tepasha/alertinua/alertinua-c/components/map/ukraine_map_data.h

#pragma once
#include <stdint.h>

typedef struct { uint8_t x, y; } map_point_t;

typedef struct {
    const char *name;   // Ukrainian name (UTF-8), for logging only (no Cyrillic glyphs on screen)
    uint16_t point_offset;
    uint8_t  point_count;
    uint16_t color;     // RGB565, NOT byte-swapped yet
} map_region_t;

#define MAP_NUM_POINTS 921
static const map_point_t map_points[MAP_NUM_POINTS] = {
    {100,56}, {104,56}, {104,60}, {106,62}, {105,65}, {109,70}, {109,73}, {110,73}, {107,74}, {106,78},
    {100,77}, {98,79}, {97,78}, {95,77}, {94,79}, {94,77}, {93,77}, {93,76}, {91,76}, {88,73},
    {85,73}, {84,70}, {84,66}, {85,63}, {89,63}, {87,58}, {88,54}, {97,53}, {98,52}, {100,56},
    {66,23}, {67,23}, {66,26}, {67,27}, {66,31}, {69,30}, {71,33}, {70,35}, {71,36}, {70,37},
    {70,38}, {69,39}, {69,41}, {67,40}, {64,41}, {64,42}, {62,43}, {63,45}, {61,46}, {60,45},
    {58,45}, {56,44}, {56,42}, {52,41}, {51,39}, {52,38}, {48,31}, {48,30}, {47,27}, {51,27},
    {55,23}, {66,23}, {189,50}, {190,51}, {193,51}, {195,53}, {197,52}, {198,54}, {201,54}, {203,57},
    {207,57}, {206,58}, {207,61}, {205,64}, {202,65}, {203,66}, {206,67}, {205,68}, {203,68}, {202,71},
    {204,71}, {205,74}, {204,75}, {205,75}, {203,79}, {203,82}, {196,82}, {196,79}, {194,79}, {192,75},
    {190,75}, {191,74}, {189,73}, {189,67}, {186,66}, {187,63}, {185,63}, {185,62}, {186,55}, {186,54},
    {187,53}, {186,52}, {189,50}, {157,63}, {159,63}, {162,65}, {166,65}, {170,72}, {171,70}, {174,71},
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
    {"Херсонська область", 754, 45, 0x66CE},
    {"Хмельницька область", 799, 27, 0xDB0E},
    {"Черкаська область", 826, 35, 0x649B},
    {"Чернігівська область", 861, 34, 0xB6CC},
    {"Чернівецька область", 895, 26, 0xDB1B},
};

#define MAP_DISPLAY_W 240
#define MAP_DISPLAY_H 135
